DB375237/smarties/images/base_piatto.png

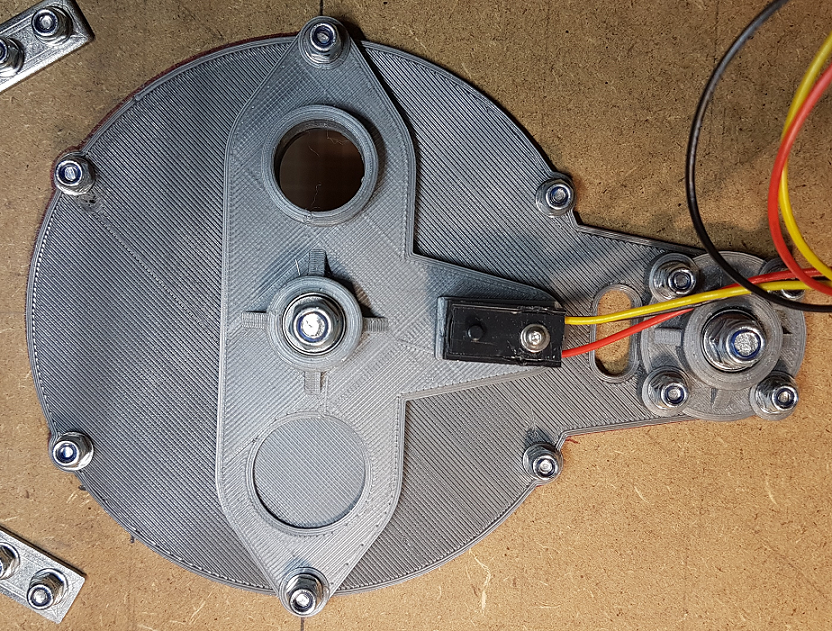
images/base_piatto.png
