DB375237/smarties/images/bottom.png

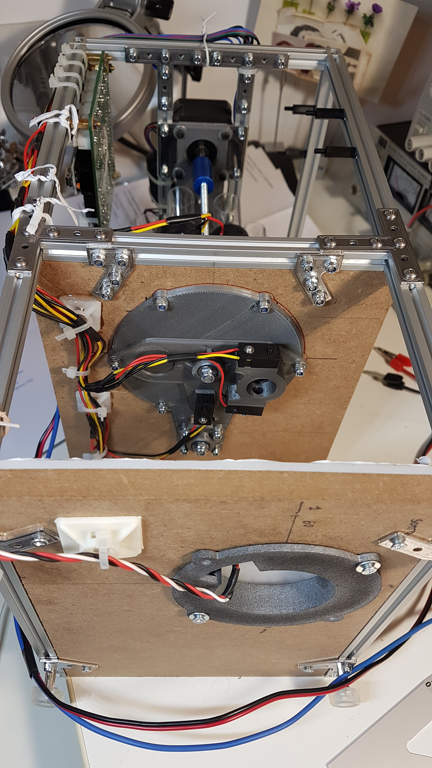
images/bottom.png
