DB375237/smarties/images/ir-barrier.png

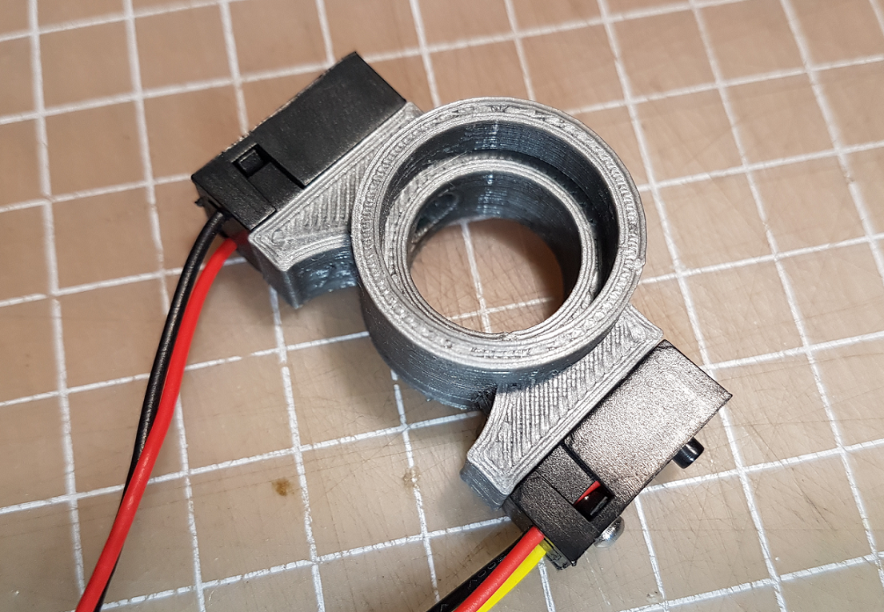
images/ir-barrier.png
