DB375237/smarties/images/platter.png

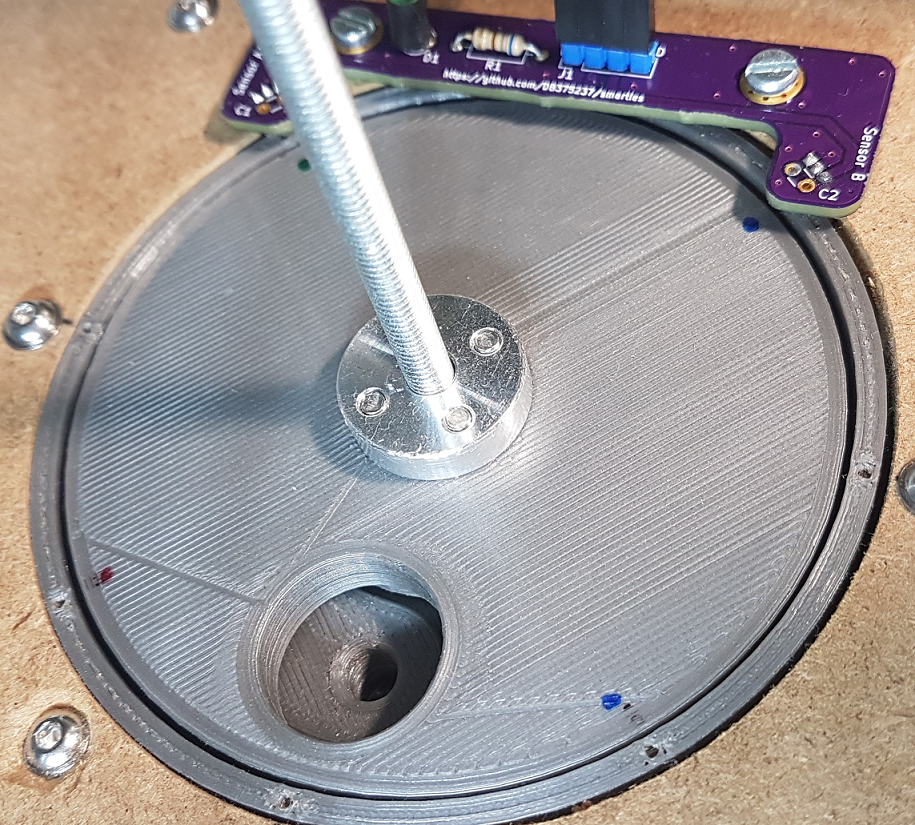
images/platter.png
