DB375237/smarties/images/stepper-spacer-02.png

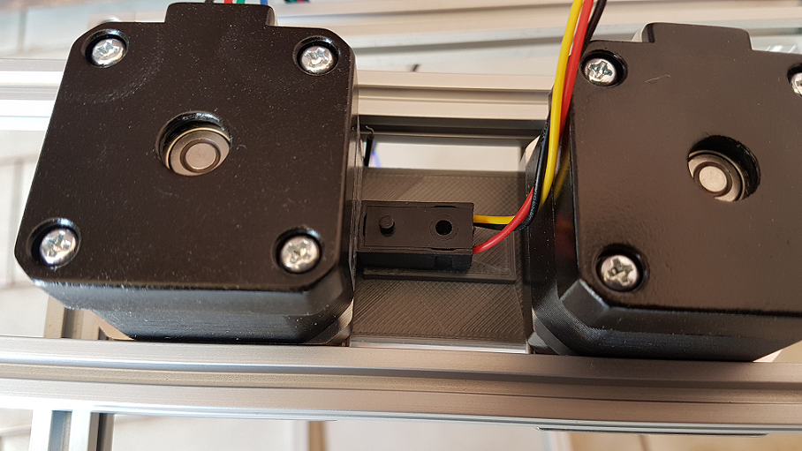
images/stepper-spacer-02.png
